JLSteenwyk/3d-printing/projects/03-narrow-flutes-tray-lamp/models/tan_base_trim_PLA.3mf

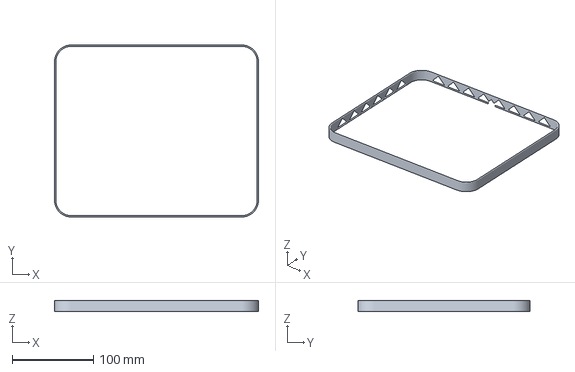
[picture p17: CAD file, 2026-10-04]
projects/03-narrow-flutes-tray-lamp/models/tan_base_trim_PLA.3mf
251.2 x 211.9 x 14.0 mm
