JLSteenwyk/3d-printing/projects/03-narrow-flutes-tray-lamp/models/olive_body_one_piece_PETG.3mf

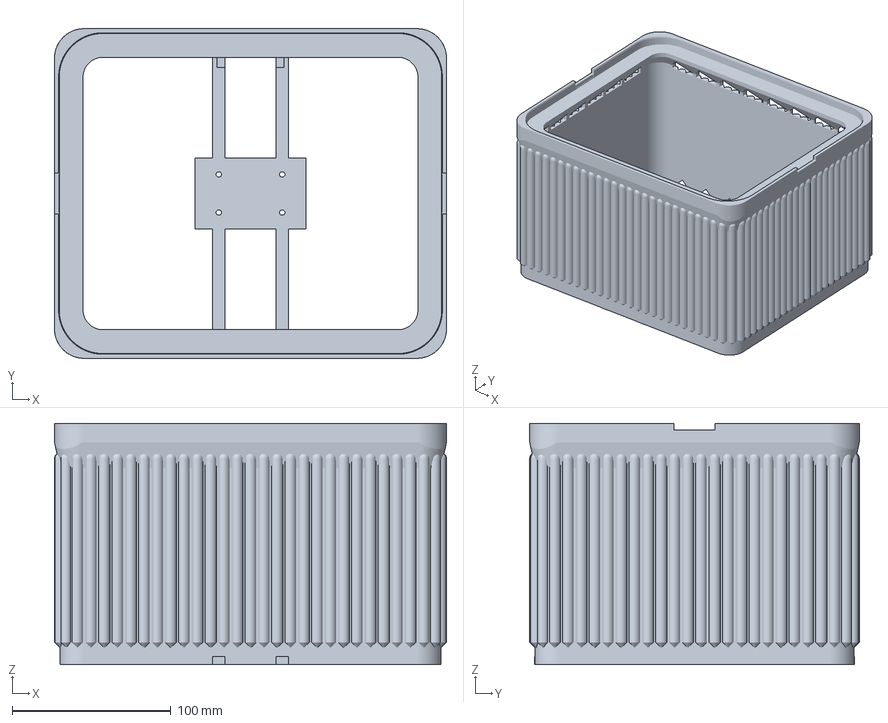
[picture p18: CAD file, 2026-10-04]
projects/03-narrow-flutes-tray-lamp/models/olive_body_one_piece_PETG.3mf
247.2 x 207.9 x 152.0 mm
