JLSteenwyk/3d-printing/projects/03-narrow-flutes-tray-lamp/models/socket_bracket_40mm_PETG.3mf

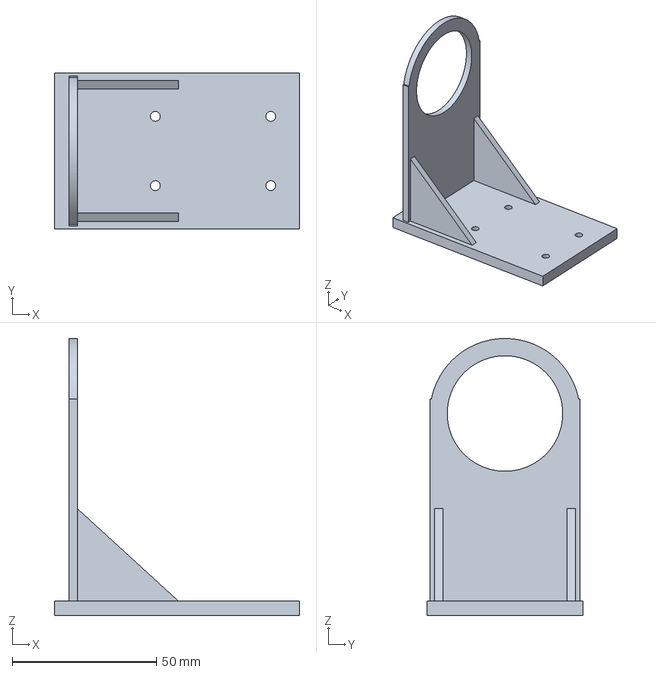
[picture p19: CAD file, 2026-10-03]
projects/03-narrow-flutes-tray-lamp/models/socket_bracket_40mm_PETG.3mf
85.0 x 54.0 x 96.0 mm
