JLSteenwyk/3d-printing/projects/03-narrow-flutes-tray-lamp/models/socket_hole_fit_gauge_37-41mm.stl

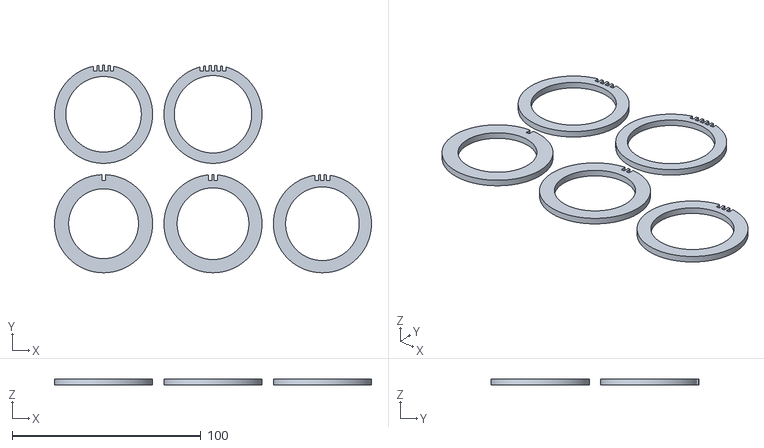
[picture p20: CAD file, 2026-10-03]
projects/03-narrow-flutes-tray-lamp/models/socket_hole_fit_gauge_37-41mm.stl
168.0 x 110.0 x 3.00
