JLSteenwyk/3d-printing/projects/03-narrow-flutes-tray-lamp/models/tray_fit_test_rim.stl

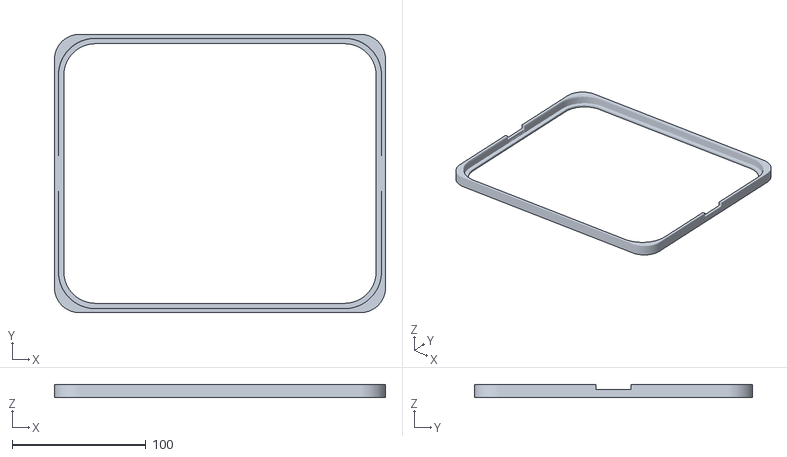
[picture p21: CAD file, 2026-10-02]
projects/03-narrow-flutes-tray-lamp/models/tray_fit_test_rim.stl
247.2 x 207.9 x 10.0
