JLSteenwyk/3d-printing/projects/03-narrow-flutes-tray-lamp/models/tray_corner_coupon.stl

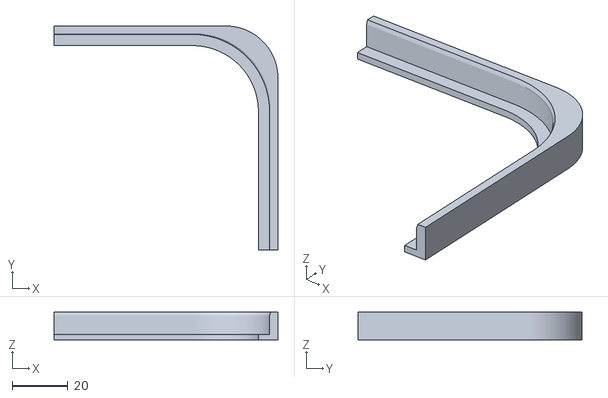
[picture p22: CAD file, 2026-10-02]
projects/03-narrow-flutes-tray-lamp/models/tray_corner_coupon.stl
80.0 x 80.0 x 10.0
